Forairaaaaa/Monica/Firmware/SourceCode/components/BMI270_BMM150/src/utilities/BMM150-Sensor-API/README.md

# BMM150 sensor API

### Sensor overview

BMM150 is a standalone geomagnetic sensor for consumer market applications.
Performance and feature of BMM150 are carefully tuned and perfectly match the
demanding requirements of all 3-axis mobile applications such as electronic
compass, navigation or augmented reality.

### Target Application
- Magnetic heading information
- Tilt-compensated electronic compass
- Gyroscope calibration in 9-DoF application for mobile devices
- In-door navigation
- Gaming

### Feature
- Magnetic field data

### Important links

- [BMM150 product page](https://www.bosch-sensortec.com/products/motion-sensors/magnetometers-bmm150/)
- [BMM150 datasheet](https://www.bosch-sensortec.com/media/boschsensortec/downloads/datasheets/bst-bmm150-ds001.pdf)
- [BMM150 shuttle board flyer](https://www.bosch-sensortec.com/media/boschsensortec/downloads/shuttle_board_flyer/bst-dhw-fl016.pdf)
- [Community support page](https://community.bosch-sensortec.com)

---
#### Copyright (C) 2020 Bosch Sensortec GmbH
