Forairaaaaa/Monica/Firmware/SourceCode/components/lvgl/rlottie/.Gifs/1.gif

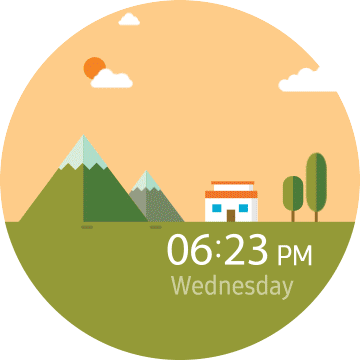
Firmware/SourceCode/components/lvgl/rlottie/.Gifs/1.gif
