Forairaaaaa/Monica/Firmware/SourceCode/main/hal/arduino/esp32-hal-ledc.c

// Copyright 2015-2016 Espressif Systems (Shanghai) PTE LTD
//
// Licensed under the Apache License, Version 2.0 (the "License");
// you may not use this file except in compliance with the License.
// You may obtain a copy of the License at

//     http://www.apache.org/licenses/LICENSE-2.0
//
// Unless required by applicable law or agreed to in writing, software
// distributed under the License is distributed on an "AS IS" BASIS,
// WITHOUT WARRANTIES OR CONDITIONS OF ANY KIND, either express or implied.
// See the License for the specific language governing permissions and
// limitations under the License.

#include "esp32-hal.h"
#include "soc/soc_caps.h"
#include "driver/ledc.h"
#include "esp32-hal-periman.h"

#ifdef SOC_LEDC_SUPPORT_HS_MODE
#define LEDC_CHANNELS           (SOC_LEDC_CHANNEL_NUM<<1)
#else
#define LEDC_CHANNELS           (SOC_LEDC_CHANNEL_NUM)
#endif

//Use XTAL clock if possible to avoid timer frequency error when setting APB clock < 80 Mhz
//Need to be fixed in ESP-IDF
#ifdef SOC_LEDC_SUPPORT_XTAL_CLOCK
#define LEDC_DEFAULT_CLK        LEDC_USE_XTAL_CLK
#else
#define LEDC_DEFAULT_CLK        LEDC_AUTO_CLK
#endif

#define LEDC_MAX_BIT_WIDTH      SOC_LEDC_TIMER_BIT_WIDE_NUM


typedef struct {
    int used_channels : LEDC_CHANNELS;              // Used channels as a bits
} ledc_periph_t;

/*
 * LEDC Chan to Group/Channel/Timer Mapping
** ledc: 0  => Group: 0, Channel: 0, Timer: 0
** ledc: 1  => Group: 0, Channel: 1, Timer: 0
** ledc: 2  => Group: 0, Channel: 2, Timer: 1
** ledc: 3  => Group: 0, Channel: 3, Timer: 1
** ledc: 4  => Group: 0, Channel: 4, Timer: 2
** ledc: 5  => Group: 0, Channel: 5, Timer: 2
** ledc: 6  => Group: 0, Channel: 6, Timer: 3
** ledc: 7  => Group: 0, Channel: 7, Timer: 3
** ledc: 8  => Group: 1, Channel: 0, Timer: 0
** ledc: 9  => Group: 1, Channel: 1, Timer: 0
** ledc: 10 => Group: 1, Channel: 2, Timer: 1
** ledc: 11 => Group: 1, Channel: 3, Timer: 1
** ledc: 12 => Group: 1, Channel: 4, Timer: 2
** ledc: 13 => Group: 1, Channel: 5, Timer: 2
** ledc: 14 => Group: 1, Channel: 6, Timer: 3
** ledc: 15 => Group: 1, Channel: 7, Timer: 3
*/

ledc_periph_t ledc_handle;

static bool ledcDetachBus(void * bus){
    ledc_channel_handle_t handle = (ledc_channel_handle_t)bus;
    ledc_handle.used_channels &= ~(1UL << handle->channel);
    pinMatrixOutDetach(handle->pin, false, false);
    return true;
}

bool ledcAttach(uint8_t pin, uint32_t freq, uint8_t resolution)
{
    int free_channel = ~ledc_handle.used_channels & (ledc_handle.used_channels+1);
    if (free_channel == 0 || resolution > LEDC_MAX_BIT_WIDTH)
    {
        log_e("No more LEDC channels available! (maximum %u) or bit width too big (maximum %u)", LEDC_CHANNELS, LEDC_MAX_BIT_WIDTH);
        return false;
    }

    perimanSetBusDeinit(ESP32_BUS_TYPE_LEDC, ledcDetachBus);
    ledc_channel_handle_t bus = (ledc_channel_handle_t)perimanGetPinBus(pin, ESP32_BUS_TYPE_LEDC);
    if(bus != NULL && !perimanSetPinBus(pin, ESP32_BUS_TYPE_INIT, NULL)){
        return false;
    }

    int channel = log2(free_channel & -free_channel);
    uint8_t group=(channel/8), timer=((channel/2)%4);

    ledc_timer_config_t ledc_timer = {
        .speed_mode       = group,
        .timer_num        = timer,
        .duty_resolution  = resolution,
        .freq_hz          = freq,
        .clk_cfg          = LEDC_DEFAULT_CLK
    };
    if(ledc_timer_config(&ledc_timer) != ESP_OK)
    {
        log_e("ledc setup failed!");
        return false;
    }

    uint32_t duty = ledc_get_duty(group,channel);

    ledc_channel_config_t ledc_channel = {
        .speed_mode     = group,
        .channel        = (channel%8),
        .timer_sel      = timer,
        .intr_type      = LEDC_INTR_DISABLE,
        .gpio_num       = pin,
        .duty           = duty,
        .hpoint         = 0
    };
    ledc_channel_config(&ledc_channel);

    ledc_channel_handle_t handle = malloc(sizeof(ledc_channel_handle_t));

    handle->pin = pin,
    handle->channel = channel,
    handle->channel_resolution = resolution,

    ledc_handle.used_channels |= 1UL << channel;

    if(!perimanSetPinBus(pin, ESP32_BUS_TYPE_LEDC, (void *)handle)){
        ledcDetachBus((void *)handle);
        return false;
    }

    return true;
}
bool ledcWrite(uint8_t pin, uint32_t duty)
{
    ledc_channel_handle_t bus = (ledc_channel_handle_t)perimanGetPinBus(pin, ESP32_BUS_TYPE_LEDC);
    if(bus != NULL){

        uint8_t group=(bus->channel/8), channel=(bus->channel%8);

        //Fixing if all bits in resolution is set = LEDC FULL ON
        uint32_t max_duty = (1 << bus->channel_resolution) - 1;

        if((duty == max_duty) && (max_duty != 1)){
            duty = max_duty + 1;
        }

        ledc_set_duty(group, channel, duty);
        ledc_update_duty(group, channel);

        return true;
    }
    return false;
}

uint32_t ledcRead(uint8_t pin)
{
    ledc_channel_handle_t bus = (ledc_channel_handle_t)perimanGetPinBus(pin, ESP32_BUS_TYPE_LEDC);
    if(bus != NULL){

        uint8_t group=(bus->channel/8), channel=(bus->channel%8);
        return ledc_get_duty(group,channel);
    }
    return 0;   
}

uint32_t ledcReadFreq(uint8_t pin)
{
    ledc_channel_handle_t bus = (ledc_channel_handle_t)perimanGetPinBus(pin, ESP32_BUS_TYPE_LEDC);
    if(bus != NULL){
        if(!ledcRead(pin)){
            return 0;
        }
        uint8_t group=(bus->channel/8), timer=((bus->channel/2)%4);
        return ledc_get_freq(group,timer);
        }
    return 0;  
}


uint32_t ledcWriteTone(uint8_t pin, uint32_t freq)
{
    ledc_channel_handle_t bus = (ledc_channel_handle_t)perimanGetPinBus(pin, ESP32_BUS_TYPE_LEDC);
    if(bus != NULL){

        if(!freq){
            ledcWrite(pin, 0);
            return 0;
        }

        uint8_t group=(bus->channel/8), timer=((bus->channel/2)%4);

        ledc_timer_config_t ledc_timer = {
            .speed_mode       = group,
            .timer_num        = timer,
            .duty_resolution  = 10,
            .freq_hz          = freq, 
            .clk_cfg          = LEDC_DEFAULT_CLK
        };

        if(ledc_timer_config(&ledc_timer) != ESP_OK)
        {
            log_e("ledcWriteTone configuration failed!");
            return 0;
        }
        bus->channel_resolution = 10;

        uint32_t res_freq = ledc_get_freq(group,timer);
        ledcWrite(pin, 0x1FF);
        return res_freq;
    }
    return 0;
}

uint32_t ledcWriteNote(uint8_t pin, note_t note, uint8_t octave){
    const uint16_t noteFrequencyBase[12] = {
    //   C        C#       D        Eb       E        F       F#        G       G#        A       Bb        B
        4186,    4435,    4699,    4978,    5274,    5588,    5920,    6272,    6645,    7040,    7459,    7902
    };

    if(octave > 8 || note >= NOTE_MAX){
        return 0;
    }
    uint32_t noteFreq =  (uint32_t)noteFrequencyBase[note] / (uint32_t)(1 << (8-octave));
    return ledcWriteTone(pin, noteFreq);
}

bool ledcDetach(uint8_t pin)
{
    ledc_channel_handle_t bus = (ledc_channel_handle_t)perimanGetPinBus(pin, ESP32_BUS_TYPE_LEDC);
    if(bus != NULL){
        // will call ledcDetachBus
        return perimanSetPinBus(pin, ESP32_BUS_TYPE_INIT, NULL);
    } else {
        log_e("pin %u is not attached to LEDC", pin);
    }
    return false;
}

uint32_t ledcChangeFrequency(uint8_t pin, uint32_t freq, uint8_t resolution)
{
    ledc_channel_handle_t bus = (ledc_channel_handle_t)perimanGetPinBus(pin, ESP32_BUS_TYPE_LEDC);
    if(bus != NULL){

        if(resolution > LEDC_MAX_BIT_WIDTH){
            log_e("LEDC resolution too big (maximum %u)", LEDC_MAX_BIT_WIDTH);
            return 0;
        }
        uint8_t group=(bus->channel/8), timer=((bus->channel/2)%4);

        ledc_timer_config_t ledc_timer = {
            .speed_mode       = group,
            .timer_num        = timer,
            .duty_resolution  = resolution,
            .freq_hz          = freq, 
            .clk_cfg          = LEDC_DEFAULT_CLK
        };

        if(ledc_timer_config(&ledc_timer) != ESP_OK)
        {
            log_e("ledcChangeFrequency failed!");
            return 0;
        }
        bus->channel_resolution = resolution;
        return ledc_get_freq(group,timer);
    }
    return 0;
}

static uint8_t analog_resolution = 8;
static int analog_frequency = 1000;
void analogWrite(uint8_t pin, int value) {
  // Use ledc hardware for internal pins
  if (pin < SOC_GPIO_PIN_COUNT) {
    ledc_channel_handle_t bus = (ledc_channel_handle_t)perimanGetPinBus(pin, ESP32_BUS_TYPE_LEDC);
    if(bus == NULL && perimanSetPinBus(pin, ESP32_BUS_TYPE_INIT, NULL)){
        if(ledcAttach(pin, analog_frequency, analog_resolution) == 0){
            log_e("analogWrite setup failed (freq = %u, resolution = %u). Try setting different resolution or frequency");
            return;
        }
    }
    ledcWrite(pin, value);
  }
}

void analogWriteFrequency(uint8_t pin, uint32_t freq) {
    if (ledcChangeFrequency(pin, freq, analog_resolution) == 0){
        log_e("analogWrite frequency cant be set due to selected resolution! Try to adjust resolution first");
        return;
    }
    analog_frequency = freq;
}

void analogWriteResolution(uint8_t pin, uint8_t resolution) {
    if (ledcChangeFrequency(pin, analog_frequency, resolution) == 0){
        log_e("analogWrite resolution cant be set due to selected frequency! Try to adjust frequency first");
        return;
    }
    analog_resolution = resolution;
}
