Forairaaaaa/Monica/Firmware/SourceCode/main/hal/button/Button.cpp

/*
	Button - a small library for Arduino to handle button debouncing
	
	MIT licensed.
*/

#include "Button.h"
// #include <Arduino.h>
#include <esp_timer.h>


#define millis() (esp_timer_get_time() / 1000)
#define digitalRead(pin) (bool)gpio_get_level(pin)


Button::Button(gpio_num_t pin, uint16_t debounce_ms)
:  _pin(pin)
,  _delay(debounce_ms)
,  _state(1)
,  _ignore_until(0)
,  _has_changed(false)
{
}

void Button::begin()
{
	// pinMode(_pin, INPUT_PULLUP);

    gpio_reset_pin(_pin);
    gpio_set_direction(_pin, GPIO_MODE_INPUT);
    gpio_set_pull_mode(_pin, GPIO_PULLUP_ONLY);
}

// 
// public methods
// 

bool Button::read()
{
	// ignore pin changes until after this delay time
	if (_ignore_until > millis())
	{
		// ignore any changes during this period
	}
	
	// pin has changed 
	else if (digitalRead(_pin) != _state)
	{
		_ignore_until = millis() + _delay;
		_state = !_state;
		_has_changed = true;
	}
	
	return _state;
}

// has the button been toggled from on -> off, or vice versa
bool Button::toggled()
{
	read();
	return has_changed();
}

// mostly internal, tells you if a button has changed after calling the read() function
bool Button::has_changed()
{
	if (_has_changed)
	{
		_has_changed = false;
		return true;
	}
	return false;
}

// has the button gone from off -> on
bool Button::pressed()
{
	return (read() == PRESSED && has_changed());
}

// has the button gone from on -> off
bool Button::released()
{
	return (read() == RELEASED && has_changed());
}
